Dyruiz131/me507_Term_Project/CAD/linear actuator/Solenoid JF-0826B render.png

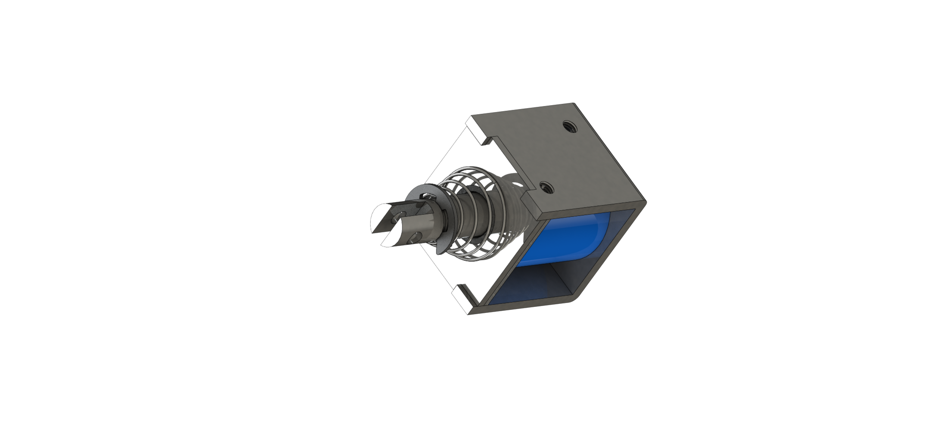
CAD/linear actuator/Solenoid JF-0826B render.png
