Dyruiz131/me507_Term_Project/CAD/V-156-1C25/Roll.SLDPRT

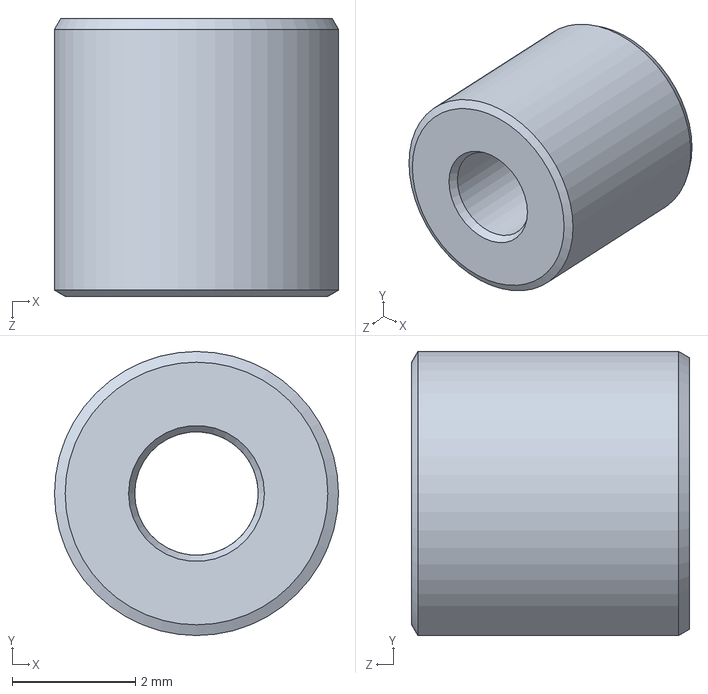
[picture p21: CAD file, 2022-11-10]
CAD/V-156-1C25/Roll.SLDPRT
4.60 x 4.60 x 4.50 mm
