Dyruiz131/me507_Term_Project/CAD/rail rail mount.SLDPRT

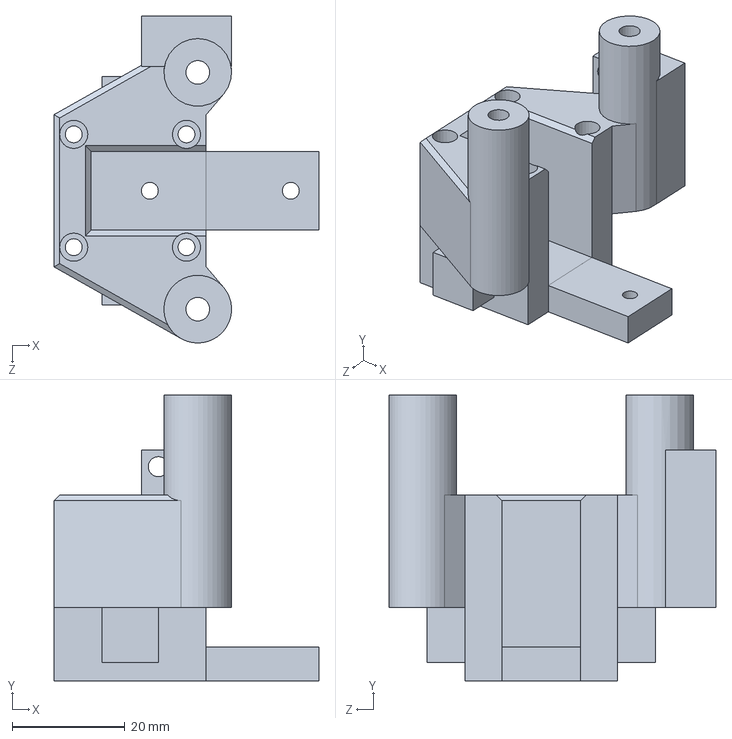
[picture p22: CAD file, 2022-11-28]
CAD/rail rail mount.SLDPRT
47.0 x 50.7 x 58.0 mm
