Dyruiz131/me507_Term_Project/CAD/V-156-1C25/Cover.SLDPRT

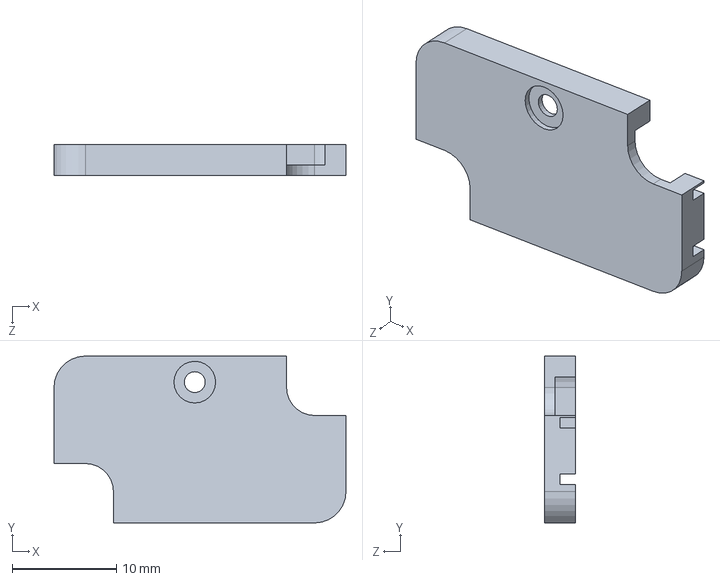
[picture p23: CAD file, 2022-11-10]
CAD/V-156-1C25/Cover.SLDPRT
28.0 x 16.0 x 3.00 mm
