Dyruiz131/me507_Term_Project/CAD/Belt Clamp.SLDPRT

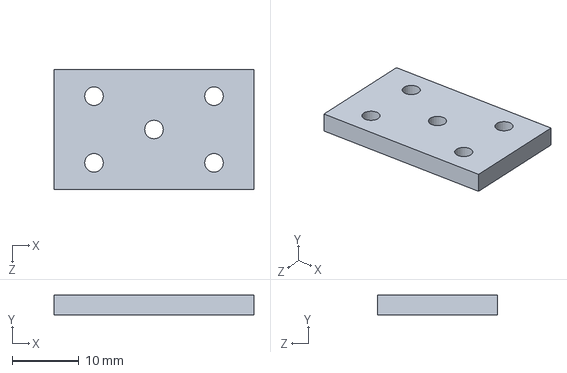
[picture p24: CAD file, 2022-11-28]
CAD/Belt Clamp.SLDPRT
30.0 x 3.00 x 18.0 mm
