Dyruiz131/me507_Term_Project/CAD/V-156-1C25/Rivet - long.SLDPRT

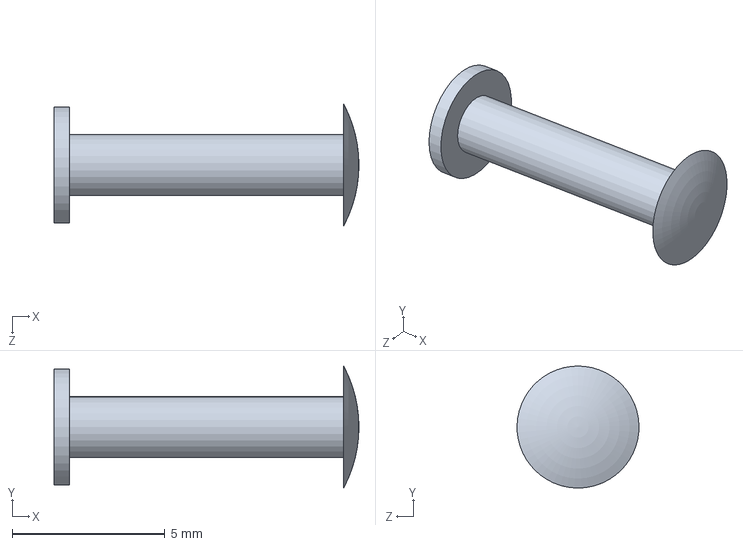
[picture p25: CAD file, 2022-11-10]
CAD/V-156-1C25/Rivet - long.SLDPRT
10.0 x 4.00 x 4.00 mm
