Dyruiz131/me507_Term_Project/CAD/MGN12H, LINEAR GUIDE BLOCK.SLDPRT

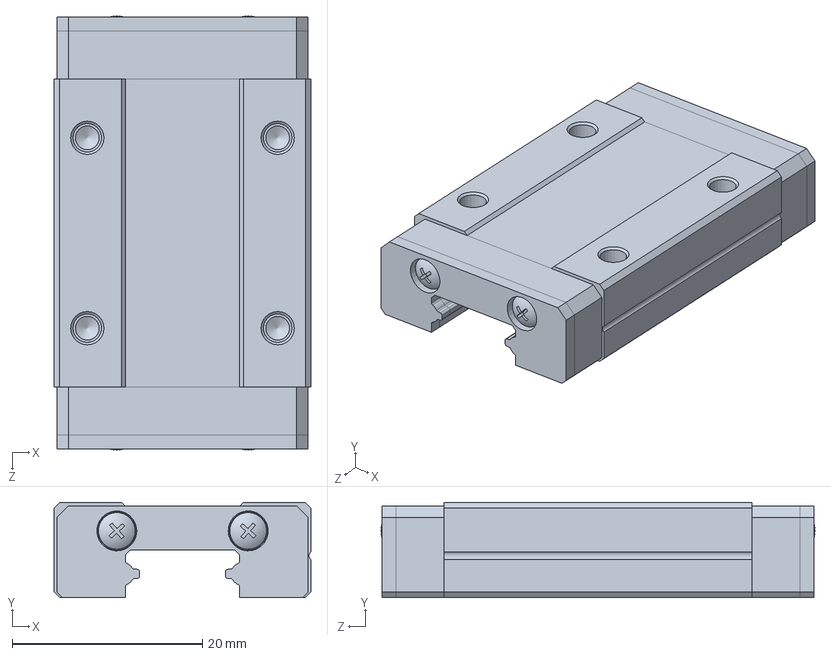
[picture p26: CAD file, 2022-11-27]
CAD/MGN12H, LINEAR GUIDE BLOCK.SLDPRT
27.0 x 10.0 x 45.6 mm
