Dyruiz131/me507_Term_Project/CAD/V-156-1C25/Switch.SLDPRT

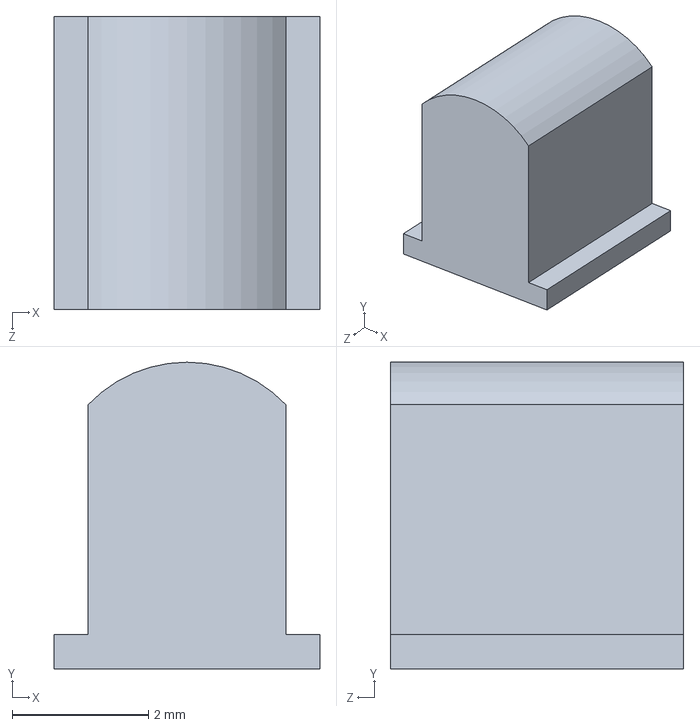
[picture p27: CAD file, 2022-11-10]
CAD/V-156-1C25/Switch.SLDPRT
3.90 x 4.50 x 4.30 mm
