Dyruiz131/me507_Term_Project/CAD/platform rail mount.SLDPRT

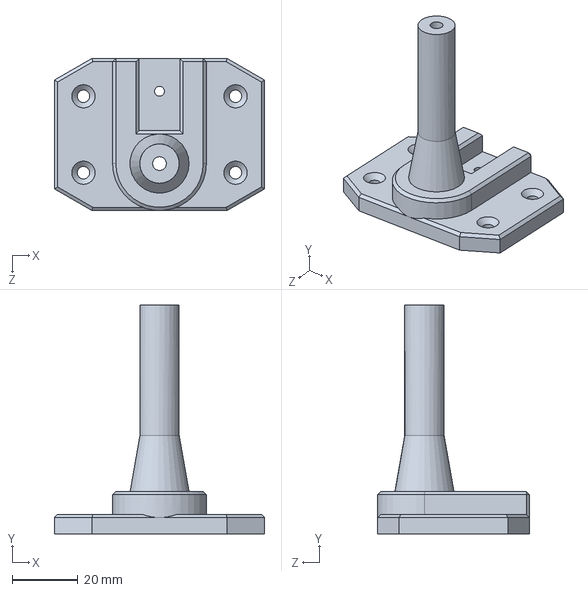
[picture p28: CAD file, 2022-11-27]
CAD/platform rail mount.SLDPRT
64.0 x 69.7 x 46.3 mm
