Dyruiz131/me507_Term_Project/CAD/V-156-1C25/Body.SLDPRT

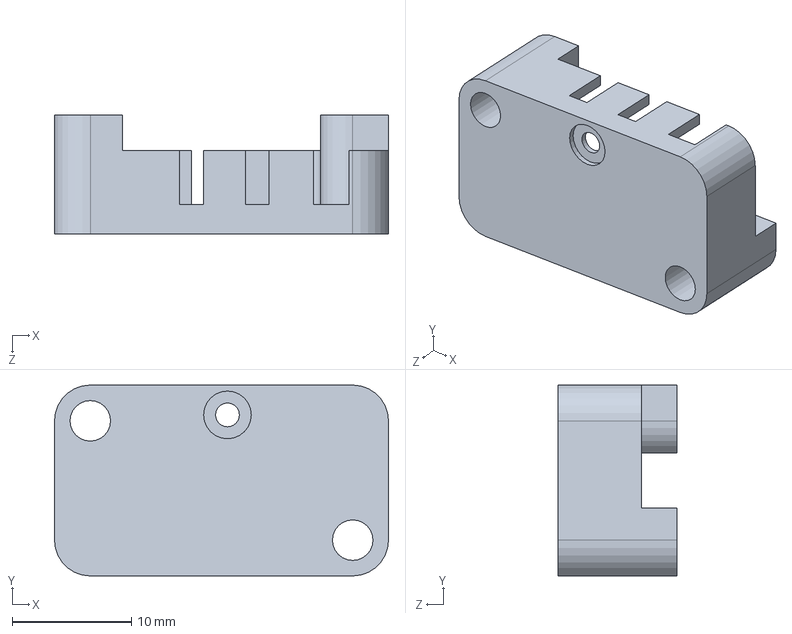
[picture p29: CAD file, 2022-11-10]
CAD/V-156-1C25/Body.SLDPRT
28.0 x 16.0 x 10.0 mm
