Dyruiz131/me507_Term_Project/CAD/platform rail mount stepper.SLDPRT

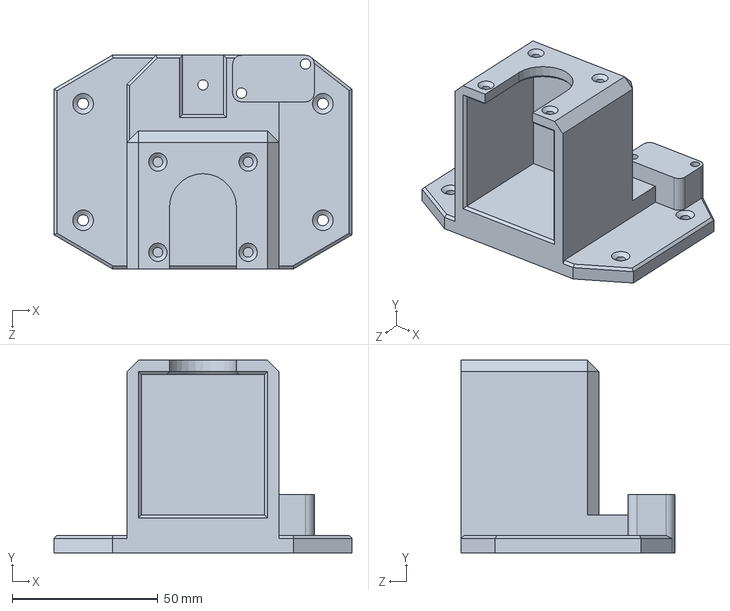
[picture p30: CAD file, 2022-11-27]
CAD/platform rail mount stepper.SLDPRT
102.3 x 66.2 x 73.3 mm
