Dyruiz131/me507_Term_Project/CAD/GT2_20T.SLDPRT

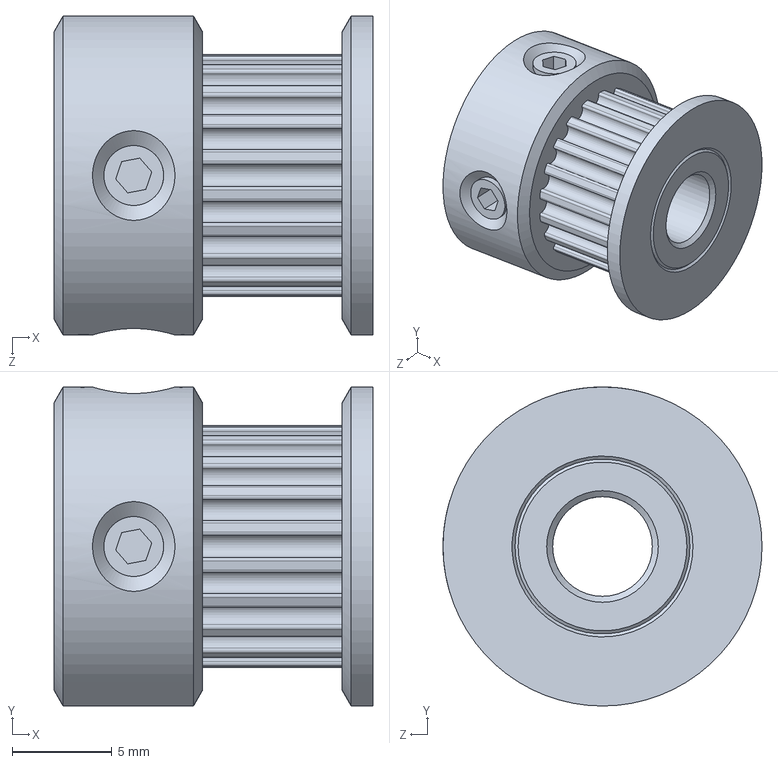
[picture p31: CAD file, 2022-11-19]
CAD/GT2_20T.SLDPRT
16.0 x 16.0 x 16.0 mm
