Dyruiz131/me507_Term_Project/CAD/GT2 idler pulley (5 mm bore) v1.SLDPRT

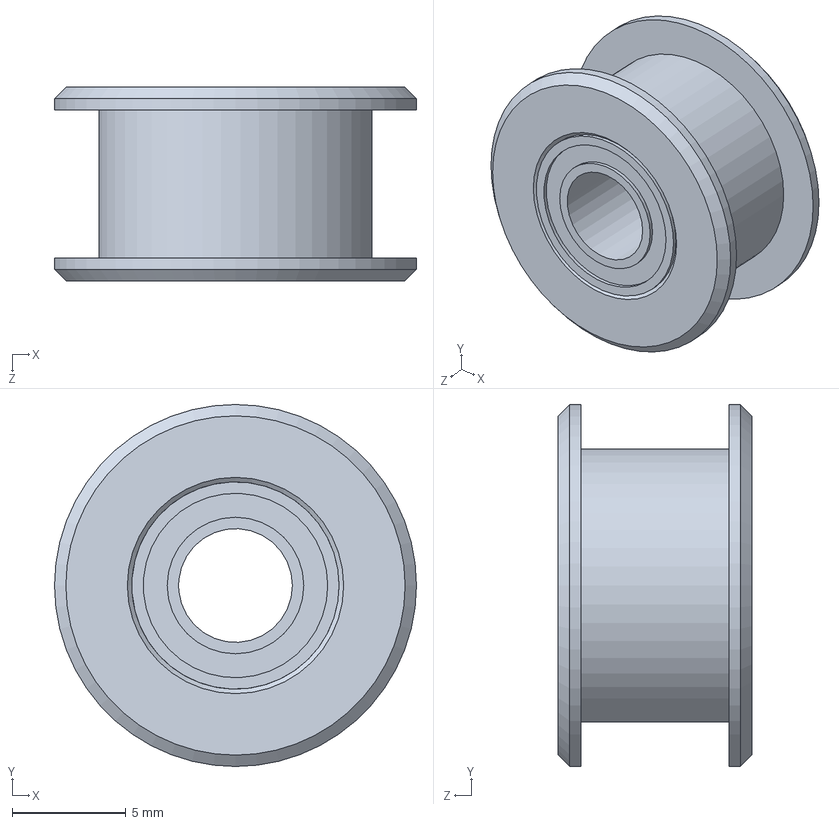
[picture p32: CAD file, 2022-11-19]
CAD/GT2 idler pulley (5 mm bore) v1.SLDPRT
15.9 x 15.9 x 8.50 mm
