Dyruiz131/me507_Term_Project/CAD/MGN12 LINEAR GUIDE RAIL, 600 mm.SLDPRT

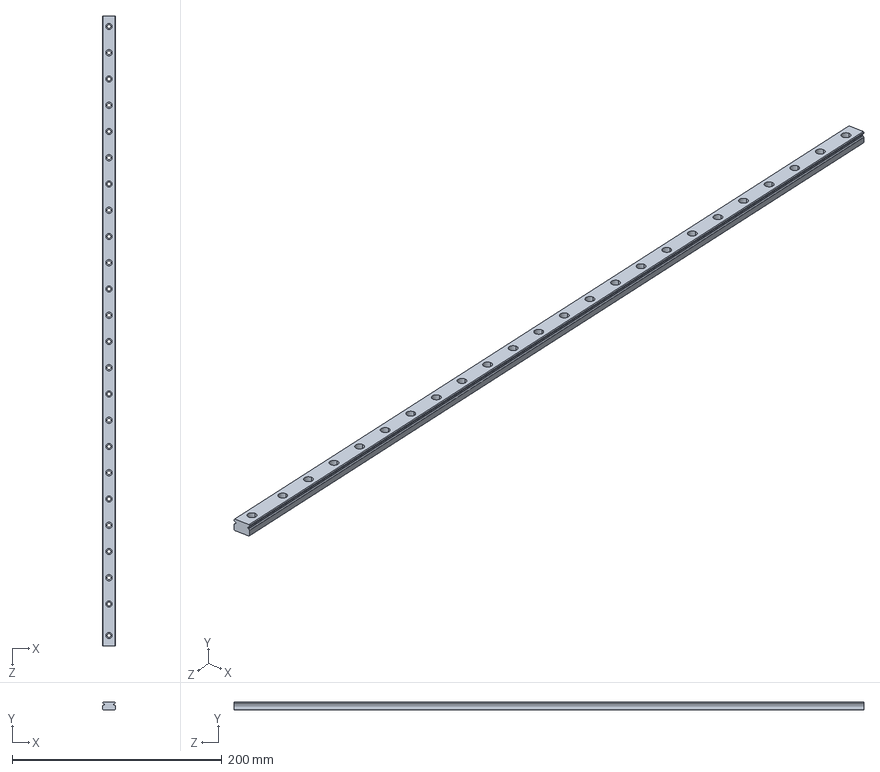
[picture p33: CAD file, 2022-11-10]
CAD/MGN12 LINEAR GUIDE RAIL, 600 mm.SLDPRT
12.0 x 8.00 x 600.0 mm
