Dyruiz131/me507_Term_Project/CAD/platform rail mount stepper bracket.SLDPRT

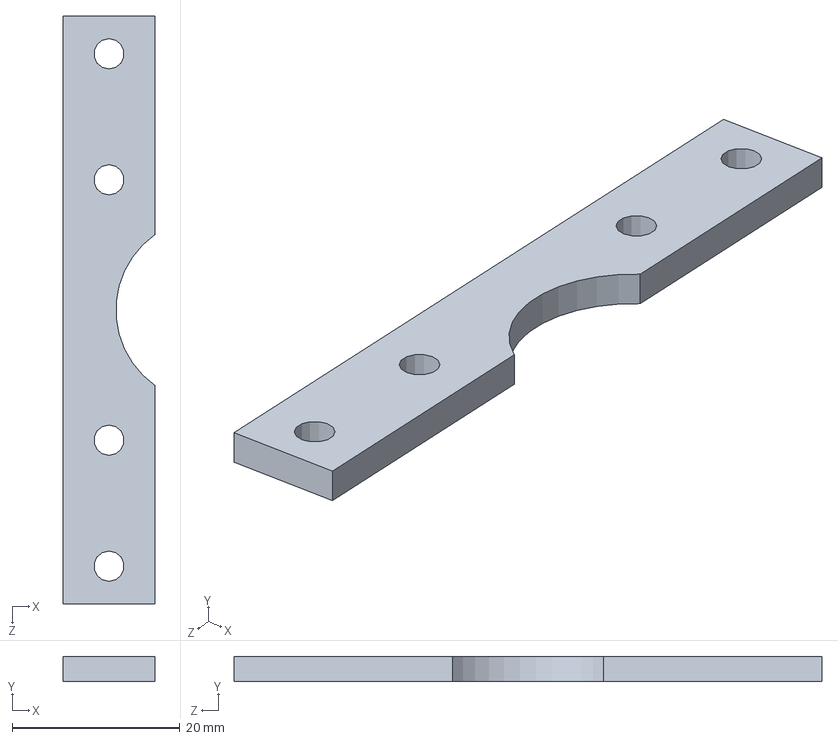
[picture p34: CAD file, 2022-11-10]
CAD/platform rail mount stepper bracket.SLDPRT
11.0 x 3.00 x 70.0 mm
