Dyruiz131/me507_Term_Project/Chessbot/src/Tasks/FetchMoveTask.h

/**
 * @file FetchMoveTask.h
 * @author Sam Hudson
 * @brief Provides the FSM that fetches moves
 * from the server and converts them to coordinates
 * (to be placed in the move queue)
 * @version 1.0
 * @date 2022-11-30
 */

#ifndef _FETCH_MOVE_TASK_H_
#define _FETCH_MOVE_TASK_H_

#include <Arduino.h>
#include "taskqueue.h"
#include "taskshare.h"
#include "objects/APIHandler.h"

class FetchMove
{
private:
    APIHandler api;
    uint8_t state;
    String lastMove;
    String newMove;
    float gridCoordinates[8];
    float gridLocations[8];
    float xOffset;
    float yOffset;
    float toCoordinate(char col);
    float toCoordinate(uint8_t row);

public:
    FetchMove(APIHandler api);
    FetchMove(); // Default constructor
    void run();  // Method for FSM
};

#endif // _FETCH_MOVE_TASK_H_
